noelmom/revlink-sidecar/web/site/assets/og-card.jpg

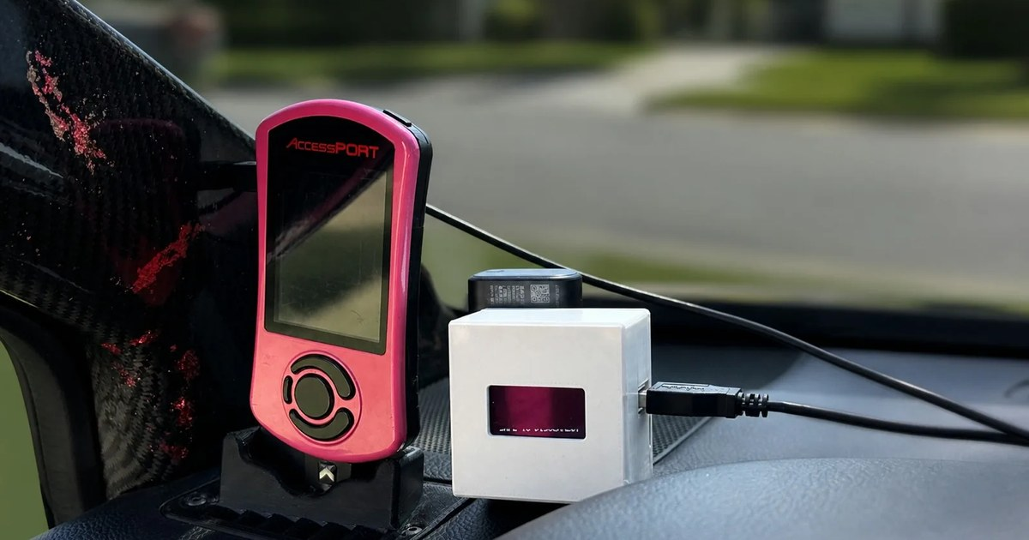
web/site/assets/og-card.jpg
