noelmom/revlink-sidecar/web/site/assets/ui-datalogs.webp

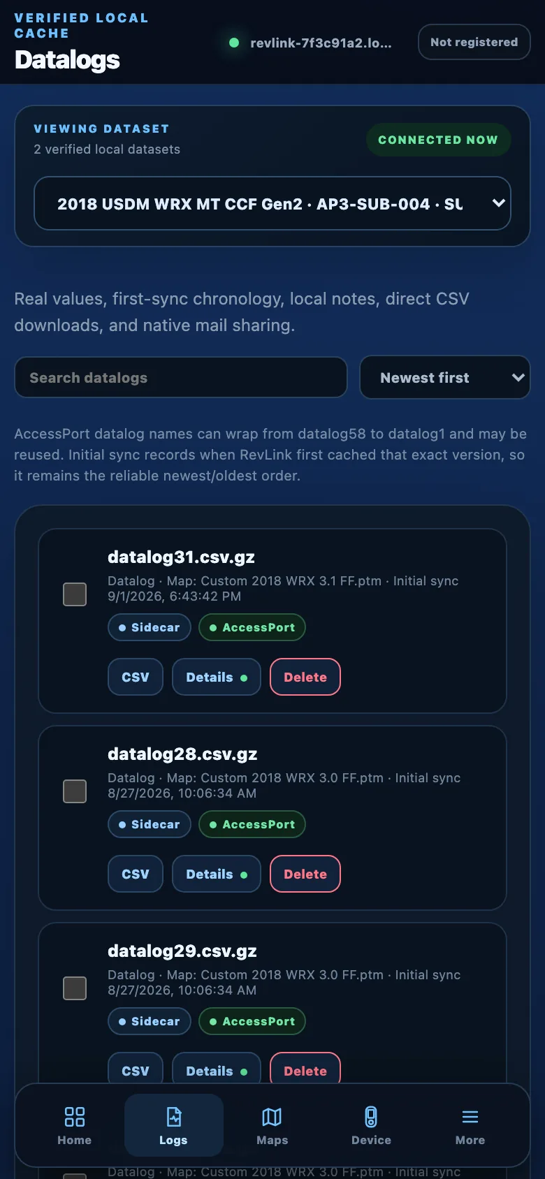
web/site/assets/ui-datalogs.webp
