noelmom/revlink-sidecar/web/site/assets/ui-maps.webp

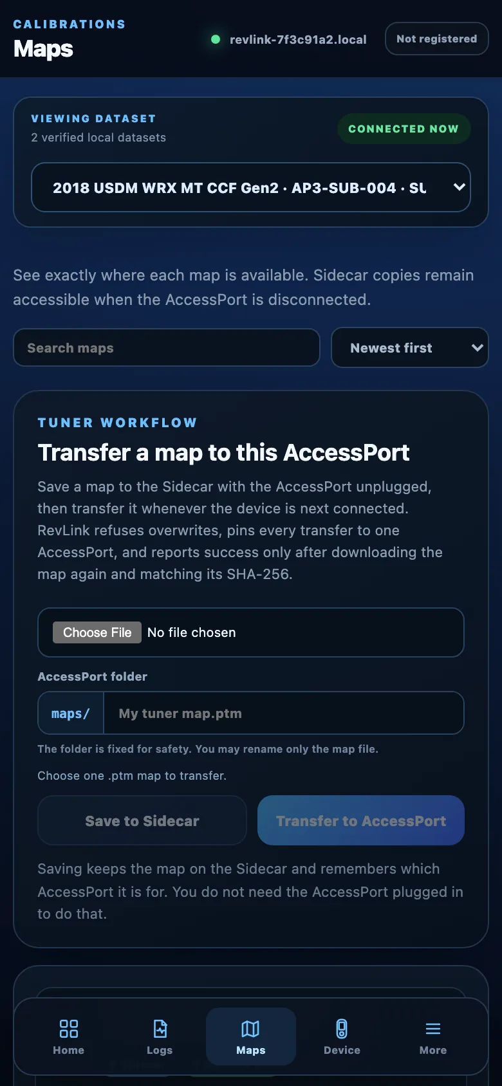
web/site/assets/ui-maps.webp
