noelmom/revlink-sidecar/hardware/nano-enclosure/enclosure-print/revlink-sidecar-nano-top-31mm-oled-preview.png

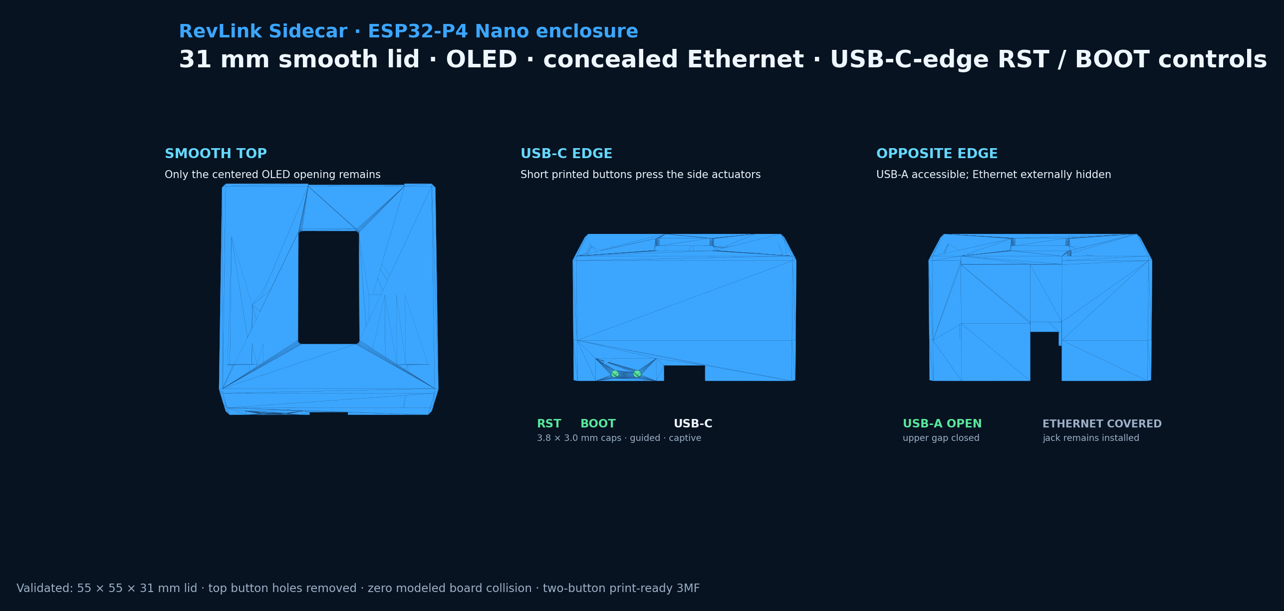
hardware/nano-enclosure/enclosure-print/revlink-sidecar-nano-top-31mm-oled-preview.png
