noelmom/revlink-sidecar/firmware/esp32p4/main/revlink_wifi_radio.c

#include "revlink_wifi_radio.h"

#include <limits.h>
#include <stdio.h>
#include <stdatomic.h>
#include <string.h>
#include <stdlib.h>

#if CONFIG_REVLINK_WIFI_SCAN_ACCEPTANCE
#include "esp_event.h"
#include "esp_netif.h"
#include "esp_wifi.h"
#include "freertos/event_groups.h"
#endif
#include "esp_log.h"
#if CONFIG_REVLINK_WIFI_JOIN_ACCEPTANCE
#include "lwip/netdb.h"
#include "lwip/ip_addr.h"
#include "ping/ping_sock.h"
#endif
#include "freertos/FreeRTOS.h"
#include "freertos/task.h"
#include "revlink_identity.h"

#define REVLINK_WIFI_SCAN_RECORD_LIMIT 24U
/*
 * Raised from 4 KiB alongside the network runtime task while chasing a stack
 * protection fault that rebooted the board every few tens of seconds, always
 * around the scan-and-join phase.
 *
 * The network task was subsequently measured and cleared — its peak use is
 * about 1.2 KiB — so if that fault was a stack overflow, this task is the
 * better suspect: it drives the esp_hosted RPC scan, whose result set is
 * assembled on this stack. The fault has not recurred since, but it has not
 * been reproduced and attributed either, so this is a suspicion, not a
 * diagnosis. The high-water logging below exists to settle it if it returns.
 */
#define REVLINK_WIFI_SCAN_TASK_STACK 6144U
#define REVLINK_WIFI_HOTSPOT_STARTED_BIT BIT2
#define REVLINK_WIFI_HOTSPOT_FAILED_BIT BIT3

static portMUX_TYPE snapshot_lock = portMUX_INITIALIZER_UNLOCKED;
static revlink_wifi_radio_snapshot_t current_snapshot = {
    .state = REVLINK_WIFI_RADIO_DISABLED,
    .strongest_rssi = INT8_MIN,
};
static revlink_wifi_visible_network_t
    visible_networks[REVLINK_WIFI_VISIBLE_NETWORK_LIMIT];
static size_t visible_network_count;
#if CONFIG_REVLINK_WIFI_JOIN_ACCEPTANCE
static bool local_identity_ready;
static char local_identity_ssid[REVLINK_IDENTITY_SSID_CAPACITY];
static char local_identity_hostname[REVLINK_IDENTITY_HOSTNAME_CAPACITY];
static uint16_t preferred_collision_index;
#endif

static void publish_snapshot(
    revlink_wifi_radio_state_t state,
    uint16_t access_point_count,
    int8_t strongest_rssi,
    uint8_t strongest_channel,
    esp_err_t last_error
)
{
    taskENTER_CRITICAL(&snapshot_lock);
    const uint8_t hotspot_client_count =
        state == REVLINK_WIFI_RADIO_HOTSPOT_READY
        || state == REVLINK_WIFI_RADIO_HOTSPOT_STARTING
        ? current_snapshot.hotspot_client_count
        : 0U;
    current_snapshot = (revlink_wifi_radio_snapshot_t){
        .state = state,
        .access_point_count = access_point_count,
        .strongest_rssi = strongest_rssi,
        .strongest_channel = strongest_channel,
        .hotspot_client_count = hotspot_client_count,
        .last_error = last_error,
    };
    taskEXIT_CRITICAL(&snapshot_lock);
}

#if CONFIG_REVLINK_WIFI_JOIN_ACCEPTANCE
static void publish_hotspot_client_delta(int delta)
{
    taskENTER_CRITICAL(&snapshot_lock);
    int count = (int)current_snapshot.hotspot_client_count + delta;
    if (count < 0) {
        count = 0;
    } else if (count > UINT8_MAX) {
        count = UINT8_MAX;
    }
    current_snapshot.hotspot_client_count = (uint8_t)count;
    taskEXIT_CRITICAL(&snapshot_lock);
}
#endif

revlink_wifi_radio_snapshot_t revlink_wifi_radio_snapshot(void)
{
    revlink_wifi_radio_snapshot_t snapshot;
    taskENTER_CRITICAL(&snapshot_lock);
    snapshot = current_snapshot;
    taskEXIT_CRITICAL(&snapshot_lock);
    return snapshot;
}

size_t revlink_wifi_radio_visible_networks(
    revlink_wifi_visible_network_t *networks,
    size_t capacity
)
{
    if (networks == NULL || capacity == 0U) {
        return 0U;
    }
    taskENTER_CRITICAL(&snapshot_lock);
    const size_t count =
        visible_network_count < capacity ? visible_network_count : capacity;
    memcpy(networks, visible_networks, count * sizeof(*networks));
    taskEXIT_CRITICAL(&snapshot_lock);
    return count;
}

#if CONFIG_REVLINK_WIFI_SCAN_ACCEPTANCE
static const char *TAG = "revlink_wifi";
static atomic_bool scan_in_progress = ATOMIC_VAR_INIT(false);
static atomic_bool radio_started = ATOMIC_VAR_INIT(false);
static atomic_bool wifi_driver_started = ATOMIC_VAR_INIT(false);
static esp_netif_t *station_netif;
#if CONFIG_REVLINK_WIFI_JOIN_ACCEPTANCE
#define REVLINK_WIFI_JOIN_CONNECTED_BIT BIT0
#define REVLINK_WIFI_JOIN_FAILED_BIT BIT1

static EventGroupHandle_t join_events;
static atomic_bool join_in_progress = ATOMIC_VAR_INIT(false);
static atomic_bool onboarding_hotspot_overlap = ATOMIC_VAR_INIT(false);
static esp_netif_t *hotspot_netif;

static void clear_sensitive(void *buffer, size_t size)
{
    volatile unsigned char *cursor = buffer;
    while (size-- > 0U) {
        *cursor++ = 0U;
    }
}
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
